necro-nemesis/Perspex-Clear-Acrylic-WS2812-LED-Audio-Interactive-Light-Bar/images/6e05ce23a0b6f5a70c8b105db6ee69d1.png

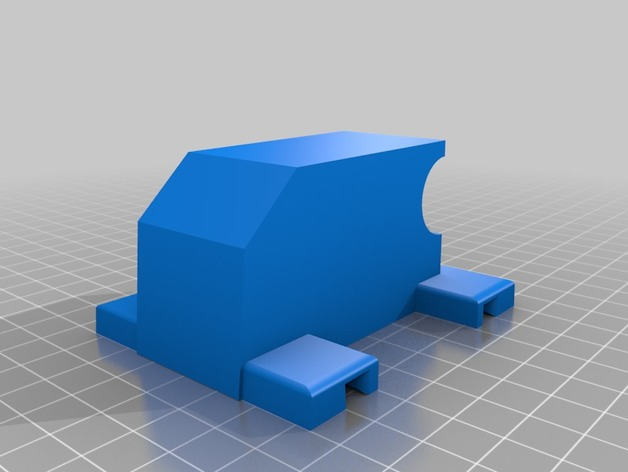
images/6e05ce23a0b6f5a70c8b105db6ee69d1.png
