necro-nemesis/Perspex-Clear-Acrylic-WS2812-LED-Audio-Interactive-Light-Bar/images/54b70367ee913e0f7b65d2cc85e12ed2.png

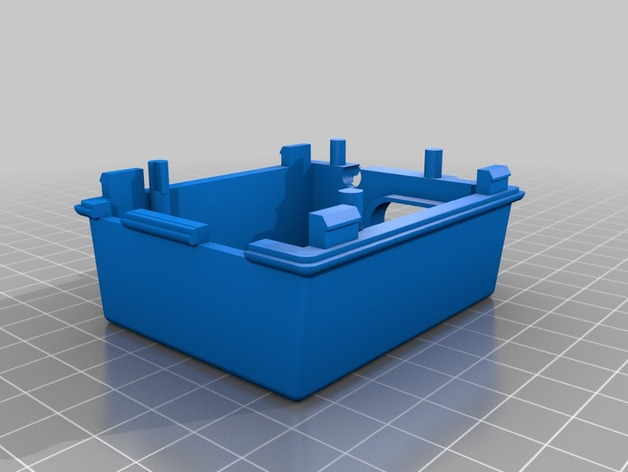
images/54b70367ee913e0f7b65d2cc85e12ed2.png
