necro-nemesis/Perspex-Clear-Acrylic-WS2812-LED-Audio-Interactive-Light-Bar/images/655aa9ce061b19eb307ddfcc23d7ef30.png

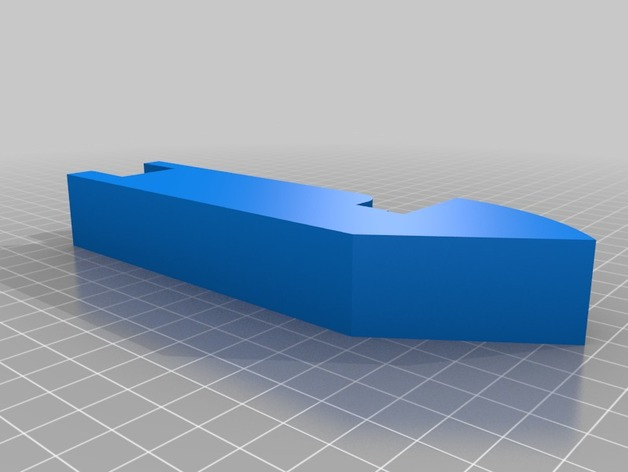
images/655aa9ce061b19eb307ddfcc23d7ef30.png
