necro-nemesis/Perspex-Clear-Acrylic-WS2812-LED-Audio-Interactive-Light-Bar/images/ac111fc5ad03a1e6dd6d8147744e5313.png

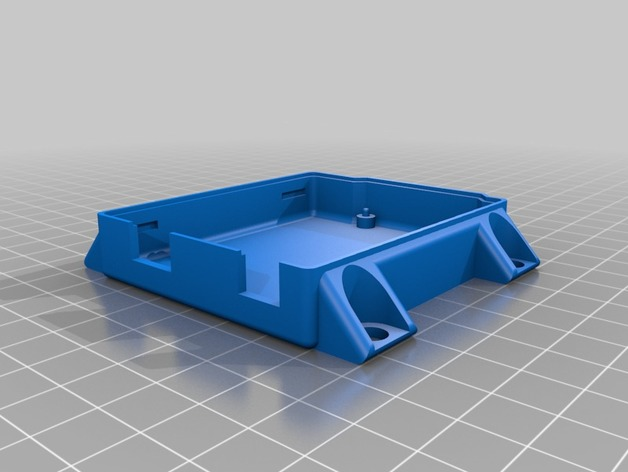
images/ac111fc5ad03a1e6dd6d8147744e5313.png
