necro-nemesis/Perspex-Clear-Acrylic-WS2812-LED-Audio-Interactive-Light-Bar/images/e53c1842df3693e8760ae6e5f5161c34.png

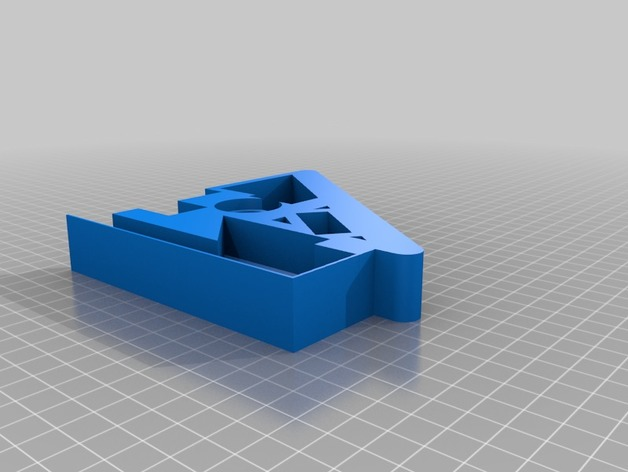
images/e53c1842df3693e8760ae6e5f5161c34.png
