necro-nemesis/Perspex-Clear-Acrylic-WS2812-LED-Audio-Interactive-Light-Bar/images/LED_Strip.PNG

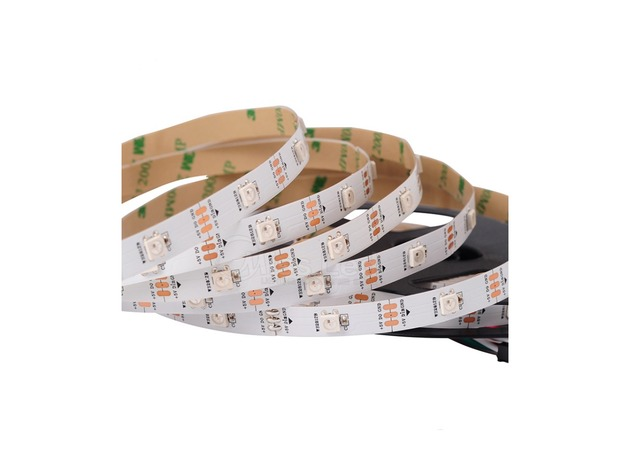
images/LED_Strip.PNG
