necro-nemesis/Perspex-Clear-Acrylic-WS2812-LED-Audio-Interactive-Light-Bar/images/pushbutton_switch.jpg

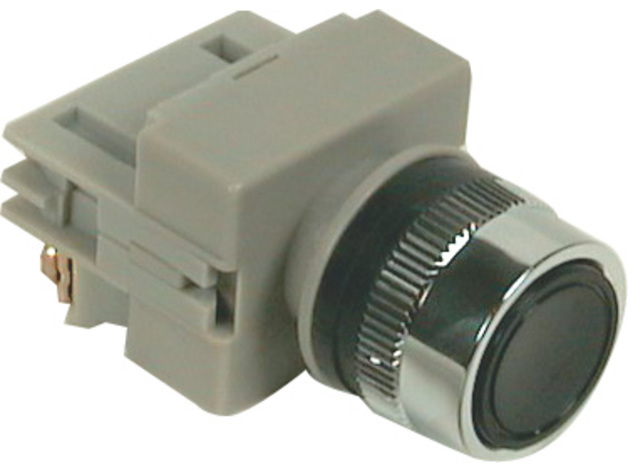
images/pushbutton_switch.jpg
