necro-nemesis/Perspex-Clear-Acrylic-WS2812-LED-Audio-Interactive-Light-Bar/images/Arduino_NeoPiixel_Wiring.PNG

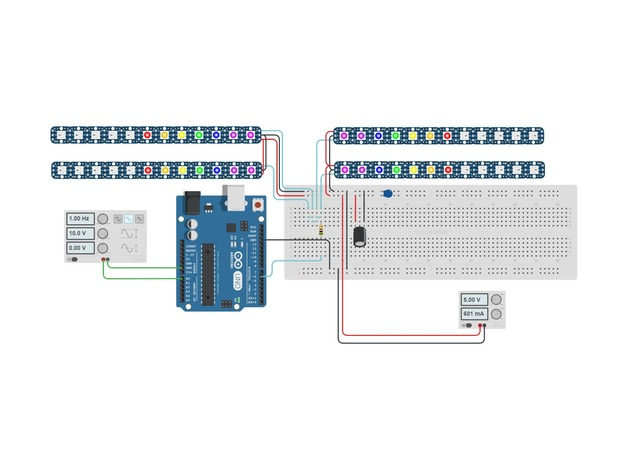
images/Arduino_NeoPiixel_Wiring.PNG
