necro-nemesis/Perspex-Clear-Acrylic-WS2812-LED-Audio-Interactive-Light-Bar/images/Underside_Assembly.png

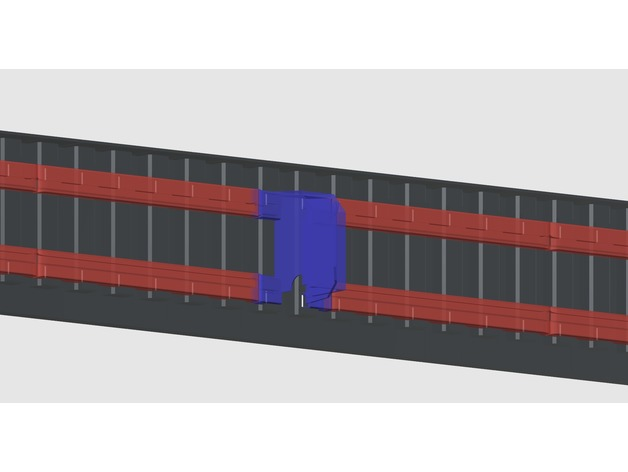
images/Underside_Assembly.png
